NguyenTran-88/Portable-Audio-Playback-Device/05_FIRMWARE/Source/Peripherals/DFPLAYER.h

/******************************************************************************************************************
@File:  	DFPlayer Mini Module
@Author:  Khue Nguyen
@Website: khuenguyencreator.com
@Youtube: https://www.youtube.com/channel/UCt8cFnPOaHrQXWmVkk-lfvg
Huong dan su dung:
- Su dung thu vien HAL
- Khoi tao UART Baud 9600
- Khoi tao bien DFPlayer : DFPLAYER_Name MP3;
- Khoi tao DFPlayer do:
	DFPLAYER_Init(&MP3, &huart1);
- Su dung cac ham phai truyen dia chi cua DFPlayer do: 
	DFPLAYER_Play(&MP3);
******************************************************************************************************************/
#ifndef __DFPLAYER_H
#define __DFPLAYER_H
#include "stm32f4xx_hal.h"

typedef struct
{
	UART_HandleTypeDef* DFP_UART;
	uint8_t SendBuff[10];
	uint16_t Checksum;
}DFPLAYER_Name;

#define DFP_PLAYTRACK 				0X12
#define DFP_NEXT 							0X01
#define DFP_PREV		  				0X02
#define DFP_SETVOLUME 				0X06
#define DFP_PLAY		 				 	0X0D
#define DFP_PAUSE		 				  0X0E
#define DFP_STOP					  	0X16
#define DFP_RANDOM 						0X18
#define DFP_PLAYFILEINFOLDER  0X0F

#define DFP_SELECT_SOURCE             0x09
#define DFP_QUERY_CUR_TF_TRACK        0x4B

#define DFP_DEVICE_TF                 0x02

void DFPLAYER_Init(DFPLAYER_Name* MP3, UART_HandleTypeDef* UART);
void DFPLAYER_PlayTrack(DFPLAYER_Name* MP3, uint16_t num);
void DFPLAYER_Next(DFPLAYER_Name* MP3);
void DFPLAYER_Prev(DFPLAYER_Name* MP3);
void DFPLAYER_SetVolume(DFPLAYER_Name* MP3, uint16_t volume);
void DFPLAYER_Play(DFPLAYER_Name* MP3);
void DFPLAYER_Pause(DFPLAYER_Name* MP3);
void DFPLAYER_Stop(DFPLAYER_Name* MP3);
void DFPLAYER_RandomPlay(DFPLAYER_Name* MP3);
void DFPLAYER_PlayFileInFolder(DFPLAYER_Name* MP3, uint8_t folder, uint32_t num);
void DFPLAYER_SelectTF(DFPLAYER_Name* MP3);
uint8_t DFPLAYER_QueryCurrentTfTrack(DFPLAYER_Name* MP3, uint16_t *track_out, uint32_t timeout_ms);

#endif
