NguyenTran-88/Portable-Audio-Playback-Device/05_FIRMWARE/Source/Peripherals/ui_assets.h

/*
 *  ui_assets.h
 *
 */

#ifndef INC_UI_ASSETS_H_
#define INC_UI_ASSETS_H_
#ifndef UI_ASSETS_H
#define UI_ASSETS_H

#include <stdint.h>

/* Main UI bitmaps */
extern const uint8_t ui_pause_bitmap[];
extern const uint8_t ui_play_bitmap[];
extern const uint8_t ui_bluetooth_bitmap[];

/* Wave animation bitmaps */
extern const uint8_t ui_wave_1[];
extern const uint8_t ui_wave_2[];
extern const uint8_t ui_wave_3[];
extern const uint8_t ui_wave_4[];
extern const uint8_t ui_wave_5[];
extern const uint8_t ui_wave_6[];
extern const uint8_t ui_wave_7[];
extern const uint8_t ui_wave_8[];
extern const uint8_t ui_wave_9[];
extern const uint8_t ui_wave_10[];
extern const uint8_t ui_wave_11[];

#endif


#endif /* INC_UI_ASSETS_H_ */
